scottalmond/NamePlate/src/jtag2updi/JTAG2.h

/*
 * packet.h
 *
 * Created: 12-11-2017 11:10:31
 *  Author: JMR_2
 */


#ifndef JTAG2_H_
#define JTAG2_H_

#include "sys.h"

namespace JTAG2 {

	// *** Parameter IDs ***
	enum parameter {
		PARAM_HW_VER				= 0x01,
		PARAM_FW_VER				= 0x02,
		PARAM_EMU_MODE				= 0x03,
		PARAM_BAUD_RATE				= 0x05,
		PARAM_VTARGET				= 0x06
	};

	// *** valid values for PARAM_BAUD_RATE_VAL
	enum baud_rate {
		baud_2400	= 0x01,
		baud_4800,
		baud_9600,
		baud_19200,				// default
		baud_38400,
		baud_57600,
		baud_115200,
		baud_14400
	};

	// *** Parameter Values ***
	constexpr uint8_t PARAM_HW_VER_M_VAL			= 0x01;
	constexpr uint8_t PARAM_HW_VER_S_VAL			= 0x01;
	constexpr uint8_t PARAM_FW_VER_M_MIN_VAL		= 0x00;
	constexpr uint8_t PARAM_FW_VER_M_MAJ_VAL		= 0x06;
	constexpr uint8_t PARAM_FW_VER_S_MIN_VAL		= 0x00;
	constexpr uint8_t PARAM_FW_VER_S_MAJ_VAL		= 0x06;
	extern uint8_t PARAM_EMU_MODE_VAL;
	extern uint8_t ConnectedTo;
	extern baud_rate PARAM_BAUD_RATE_VAL;
	constexpr uint16_t PARAM_VTARGET_VAL			= 5000;

	// *** General command constants ***
	enum cmnd {
		CMND_SIGN_OFF				= 0x00,
		CMND_GET_SIGN_ON			= 0x01,
		CMND_SET_PARAMETER			= 0x02,
		CMND_GET_PARAMETER			= 0x03,
		CMND_WRITE_MEMORY			= 0x04,
		CMND_READ_MEMORY			= 0x05,
		CMND_GO						= 0x08,
		CMND_RESET					= 0x0b,
		CMND_SET_DEVICE_DESCRIPTOR	= 0x0c,
		CMND_GET_SYNC				= 0x0f,
		CMND_ENTER_PROGMODE			= 0x14,
		CMND_LEAVE_PROGMODE			= 0x15,
		CMND_XMEGA_ERASE			= 0x34
	};
	// *** JTAG Mk2 Single byte status responses ***
	enum response {
		// Success
		RSP_OK						= 0x80,
		RSP_PARAMETER				= 0x81,
		RSP_MEMORY					= 0x82,
		RSP_SIGN_ON					= 0x86,
		// Error
		RSP_FAILED					= 0xA0,
		RSP_ILLEGAL_PARAMETER		= 0xA1,
		RSP_ILLEGAL_MEMORY_TYPE		= 0xA2,
		RSP_ILLEGAL_MEMORY_RANGE	= 0xA3,
		RSP_ILLEGAL_MCU_STATE		= 0xA5,
		RSP_ILLEGAL_VALUE			= 0xA6,
		RSP_ILLEGAL_BREAKPOINT		= 0xA8,
		RSP_ILLEGAL_JTAG_ID			= 0xA9,
		RSP_ILLEGAL_COMMAND			= 0xAA,
		RSP_NO_TARGET_POWER			= 0xAB,
		RSP_DEBUGWIRE_SYNC_FAILED	= 0xAC,
		RSP_ILLEGAL_POWER_STATE		= 0xAD
	};

	// *** memory types for CMND_{READ,WRITE}_MEMORY ***
	enum mem_type {
		MTYPE_IO_SHADOW				= 0x30,		// cached IO registers?
		MTYPE_SRAM					= 0x20,		// target's SRAM or [ext.] IO registers
		MTYPE_EEPROM				= 0x22,		// EEPROM, what way?
		MTYPE_EVENT					= 0x60,		// ICE event memory
		MTYPE_SPM					= 0xA0,		// flash through LPM/SPM
		MTYPE_FLASH_PAGE			= 0xB0,		// flash in programming mode
		MTYPE_EEPROM_PAGE			= 0xB1,		// EEPROM in programming mode
		MTYPE_FUSE_BITS				= 0xB2,		// fuse bits in programming mode
		MTYPE_LOCK_BITS				= 0xB3,		// lock bits in programming mode
		MTYPE_SIGN_JTAG				= 0xB4,		// signature in programming mode
		MTYPE_OSCCAL_BYTE			= 0xB5,		// osccal cells in programming mode
		MTYPE_CAN					= 0xB6,		// CAN mailbox
		MTYPE_FLASH					= 0xc0,		// xmega (app.) flash
		MTYPE_BOOT_FLASH			= 0xc1,		// xmega boot flash
		MTYPE_EEPROM_XMEGA			= 0xc4,		// xmega EEPROM in debug mode
		MTYPE_USERSIG				= 0xc5,		// xmega user signature
		MTYPE_PRODSIG				= 0xc6		// xmega production signature
	};

	// *** STK500 packet ***
	constexpr uint8_t MESSAGE_START = 0x1B;
	constexpr int MAX_BODY_SIZE = 700;				// Note: should not be reduced to less than 300 bytes.
	union packet_t {
		uint8_t raw[6 + MAX_BODY_SIZE];
		struct {
			union {
				uint16_t number;
				uint8_t number_byte[2];
			};
			union {
				uint32_t size;
				uint16_t size_word[2];
				uint8_t size_byte[4];
			};
			uint8_t body[MAX_BODY_SIZE];
		};
	} extern packet;
	constexpr uint8_t TOKEN = 0x0E;

	// *** Parameter initialization ***
	void init();

	// *** Packet functions ***
	bool receive();
	void answer();
	void delay_exec();

	// *** Set status function ***
	void set_status(uint8_t) __attribute__ ((noinline));

	// *** General command functions ***
	void sign_on();
	void get_parameter();
	void set_parameter();
	void set_device_descriptor();

	// *** ISP command functions ***
	void enter_progmode();
	void leave_progmode();
	void go();
	void read_signature();
	void read_mem();
	void write_mem();
	void erase();
}



#endif /* STK_H_ */
