scottalmond/NamePlate/src/test/atmel_touch_bak/atmel_touch_proj/atmel_touch_proj/include/atmel_start_pins.h

/*
 * Code generated from START.
 *
 * This file will be overwritten when reconfiguring your START project.
 * Please copy examples or other code you want to keep to a separate file
 * to avoid losing it when reconfiguring.
 */
#ifndef ATMEL_START_PINS_H_INCLUDED
#define ATMEL_START_PINS_H_INCLUDED

#include <port.h>

/**
 * \brief Set PIN_PA7 pull mode
 *
 * Configure pin to pull up, down or disable pull mode, supported pull
 * modes are defined by device used
 *
 * \param[in] pull_mode Pin pull mode
 */
static inline void PIN_PA7_set_pull_mode(const enum port_pull_mode pull_mode)
{
	PORTA_set_pin_pull_mode(7, pull_mode);
}

/**
 * \brief Set PIN_PA7 data direction
 *
 * Select if the pin data direction is input, output or disabled.
 * If disabled state is not possible, this function throws an assert.
 *
 * \param[in] direction PORT_DIR_IN  = Data direction in
 *                      PORT_DIR_OUT = Data direction out
 *                      PORT_DIR_OFF = Disables the pin
 *                      (low power state)
 */
static inline void PIN_PA7_set_dir(const enum port_dir dir)
{
	PORTA_set_pin_dir(7, dir);
}

/**
 * \brief Set PIN_PA7 input/sense configuration
 *
 * Enable/disable PIN_PA7 digital input buffer and pin change interrupt,
 * select pin interrupt edge/level sensing mode
 *
 * \param[in] isc PORT_ISC_INTDISABLE_gc    = Iterrupt disabled but input buffer enabled
 *                PORT_ISC_BOTHEDGES_gc     = Sense Both Edges
 *                PORT_ISC_RISING_gc        = Sense Rising Edge
 *                PORT_ISC_FALLING_gc       = Sense Falling Edge
 *                PORT_ISC_INPUT_DISABLE_gc = Digital Input Buffer disabled
 *                PORT_ISC_LEVEL_gc         = Sense low Level
 */
static inline void PIN_PA7_set_isc(const PORT_ISC_t isc)
{
	PORTA_pin_set_isc(7, isc);
}

/**
 * \brief Set PIN_PA7 inverted mode
 *
 * Enable or disable inverted I/O on a pin
 *
 * \param[in] inverted true  = I/O on PIN_PA7 is inverted
 *                     false = I/O on PIN_PA7 is not inverted
 */
static inline void PIN_PA7_set_inverted(const bool inverted)
{
	PORTA_pin_set_inverted(7, inverted);
}

/**
 * \brief Set PIN_PA7 level
 *
 * Sets output level on a pin
 *
 * \param[in] level true  = Pin level set to "high" state
 *                  false = Pin level set to "low" state
 */
static inline void PIN_PA7_set_level(const bool level)
{
	PORTA_set_pin_level(7, level);
}

/**
 * \brief Toggle output level on PIN_PA7
 *
 * Toggle the pin level
 */
static inline void PIN_PA7_toggle_level()
{
	PORTA_toggle_pin_level(7);
}

/**
 * \brief Get level on PIN_PA7
 *
 * Reads the level on a pin
 */
static inline bool PIN_PA7_get_level()
{
	return PORTA_get_pin_level(7);
}

/**
 * \brief Set PIN_PB0 pull mode
 *
 * Configure pin to pull up, down or disable pull mode, supported pull
 * modes are defined by device used
 *
 * \param[in] pull_mode Pin pull mode
 */
static inline void PIN_PB0_set_pull_mode(const enum port_pull_mode pull_mode)
{
	PORTB_set_pin_pull_mode(0, pull_mode);
}

/**
 * \brief Set PIN_PB0 data direction
 *
 * Select if the pin data direction is input, output or disabled.
 * If disabled state is not possible, this function throws an assert.
 *
 * \param[in] direction PORT_DIR_IN  = Data direction in
 *                      PORT_DIR_OUT = Data direction out
 *                      PORT_DIR_OFF = Disables the pin
 *                      (low power state)
 */
static inline void PIN_PB0_set_dir(const enum port_dir dir)
{
	PORTB_set_pin_dir(0, dir);
}

/**
 * \brief Set PIN_PB0 input/sense configuration
 *
 * Enable/disable PIN_PB0 digital input buffer and pin change interrupt,
 * select pin interrupt edge/level sensing mode
 *
 * \param[in] isc PORT_ISC_INTDISABLE_gc    = Iterrupt disabled but input buffer enabled
 *                PORT_ISC_BOTHEDGES_gc     = Sense Both Edges
 *                PORT_ISC_RISING_gc        = Sense Rising Edge
 *                PORT_ISC_FALLING_gc       = Sense Falling Edge
 *                PORT_ISC_INPUT_DISABLE_gc = Digital Input Buffer disabled
 *                PORT_ISC_LEVEL_gc         = Sense low Level
 */
static inline void PIN_PB0_set_isc(const PORT_ISC_t isc)
{
	PORTB_pin_set_isc(0, isc);
}

/**
 * \brief Set PIN_PB0 inverted mode
 *
 * Enable or disable inverted I/O on a pin
 *
 * \param[in] inverted true  = I/O on PIN_PB0 is inverted
 *                     false = I/O on PIN_PB0 is not inverted
 */
static inline void PIN_PB0_set_inverted(const bool inverted)
{
	PORTB_pin_set_inverted(0, inverted);
}

/**
 * \brief Set PIN_PB0 level
 *
 * Sets output level on a pin
 *
 * \param[in] level true  = Pin level set to "high" state
 *                  false = Pin level set to "low" state
 */
static inline void PIN_PB0_set_level(const bool level)
{
	PORTB_set_pin_level(0, level);
}

/**
 * \brief Toggle output level on PIN_PB0
 *
 * Toggle the pin level
 */
static inline void PIN_PB0_toggle_level()
{
	PORTB_toggle_pin_level(0);
}

/**
 * \brief Get level on PIN_PB0
 *
 * Reads the level on a pin
 */
static inline bool PIN_PB0_get_level()
{
	return PORTB_get_pin_level(0);
}

/**
 * \brief Set PB2 pull mode
 *
 * Configure pin to pull up, down or disable pull mode, supported pull
 * modes are defined by device used
 *
 * \param[in] pull_mode Pin pull mode
 */
static inline void PB2_set_pull_mode(const enum port_pull_mode pull_mode)
{
	PORTB_set_pin_pull_mode(2, pull_mode);
}

/**
 * \brief Set PB2 data direction
 *
 * Select if the pin data direction is input, output or disabled.
 * If disabled state is not possible, this function throws an assert.
 *
 * \param[in] direction PORT_DIR_IN  = Data direction in
 *                      PORT_DIR_OUT = Data direction out
 *                      PORT_DIR_OFF = Disables the pin
 *                      (low power state)
 */
static inline void PB2_set_dir(const enum port_dir dir)
{
	PORTB_set_pin_dir(2, dir);
}

/**
 * \brief Set PB2 input/sense configuration
 *
 * Enable/disable PB2 digital input buffer and pin change interrupt,
 * select pin interrupt edge/level sensing mode
 *
 * \param[in] isc PORT_ISC_INTDISABLE_gc    = Iterrupt disabled but input buffer enabled
 *                PORT_ISC_BOTHEDGES_gc     = Sense Both Edges
 *                PORT_ISC_RISING_gc        = Sense Rising Edge
 *                PORT_ISC_FALLING_gc       = Sense Falling Edge
 *                PORT_ISC_INPUT_DISABLE_gc = Digital Input Buffer disabled
 *                PORT_ISC_LEVEL_gc         = Sense low Level
 */
static inline void PB2_set_isc(const PORT_ISC_t isc)
{
	PORTB_pin_set_isc(2, isc);
}

/**
 * \brief Set PB2 inverted mode
 *
 * Enable or disable inverted I/O on a pin
 *
 * \param[in] inverted true  = I/O on PB2 is inverted
 *                     false = I/O on PB2 is not inverted
 */
static inline void PB2_set_inverted(const bool inverted)
{
	PORTB_pin_set_inverted(2, inverted);
}

/**
 * \brief Set PB2 level
 *
 * Sets output level on a pin
 *
 * \param[in] level true  = Pin level set to "high" state
 *                  false = Pin level set to "low" state
 */
static inline void PB2_set_level(const bool level)
{
	PORTB_set_pin_level(2, level);
}

/**
 * \brief Toggle output level on PB2
 *
 * Toggle the pin level
 */
static inline void PB2_toggle_level()
{
	PORTB_toggle_pin_level(2);
}

/**
 * \brief Get level on PB2
 *
 * Reads the level on a pin
 */
static inline bool PB2_get_level()
{
	return PORTB_get_pin_level(2);
}

/**
 * \brief Set PB3 pull mode
 *
 * Configure pin to pull up, down or disable pull mode, supported pull
 * modes are defined by device used
 *
 * \param[in] pull_mode Pin pull mode
 */
static inline void PB3_set_pull_mode(const enum port_pull_mode pull_mode)
{
	PORTB_set_pin_pull_mode(3, pull_mode);
}

/**
 * \brief Set PB3 data direction
 *
 * Select if the pin data direction is input, output or disabled.
 * If disabled state is not possible, this function throws an assert.
 *
 * \param[in] direction PORT_DIR_IN  = Data direction in
 *                      PORT_DIR_OUT = Data direction out
 *                      PORT_DIR_OFF = Disables the pin
 *                      (low power state)
 */
static inline void PB3_set_dir(const enum port_dir dir)
{
	PORTB_set_pin_dir(3, dir);
}

/**
 * \brief Set PB3 input/sense configuration
 *
 * Enable/disable PB3 digital input buffer and pin change interrupt,
 * select pin interrupt edge/level sensing mode
 *
 * \param[in] isc PORT_ISC_INTDISABLE_gc    = Iterrupt disabled but input buffer enabled
 *                PORT_ISC_BOTHEDGES_gc     = Sense Both Edges
 *                PORT_ISC_RISING_gc        = Sense Rising Edge
 *                PORT_ISC_FALLING_gc       = Sense Falling Edge
 *                PORT_ISC_INPUT_DISABLE_gc = Digital Input Buffer disabled
 *                PORT_ISC_LEVEL_gc         = Sense low Level
 */
static inline void PB3_set_isc(const PORT_ISC_t isc)
{
	PORTB_pin_set_isc(3, isc);
}

/**
 * \brief Set PB3 inverted mode
 *
 * Enable or disable inverted I/O on a pin
 *
 * \param[in] inverted true  = I/O on PB3 is inverted
 *                     false = I/O on PB3 is not inverted
 */
static inline void PB3_set_inverted(const bool inverted)
{
	PORTB_pin_set_inverted(3, inverted);
}

/**
 * \brief Set PB3 level
 *
 * Sets output level on a pin
 *
 * \param[in] level true  = Pin level set to "high" state
 *                  false = Pin level set to "low" state
 */
static inline void PB3_set_level(const bool level)
{
	PORTB_set_pin_level(3, level);
}

/**
 * \brief Toggle output level on PB3
 *
 * Toggle the pin level
 */
static inline void PB3_toggle_level()
{
	PORTB_toggle_pin_level(3);
}

/**
 * \brief Get level on PB3
 *
 * Reads the level on a pin
 */
static inline bool PB3_get_level()
{
	return PORTB_get_pin_level(3);
}

#endif /* ATMEL_START_PINS_H_INCLUDED */
