scottalmond/NamePlate/src/test/atmel_blink/simple_blink/simple_blink/src/driver_init.c

/**
 * \file
 *
 * \brief Driver initialization.
 *
 (c) 2018 Microchip Technology Inc. and its subsidiaries.

    Subject to your compliance with these terms,you may use this software and
    any derivatives exclusively with Microchip products.It is your responsibility
    to comply with third party license terms applicable to your use of third party
    software (including open source software) that may accompany Microchip software.

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
    IN NO EVENT WILL MICROCHIP BE LIABLE FOR ANY INDIRECT, SPECIAL, PUNITIVE,
    INCIDENTAL OR CONSEQUENTIAL LOSS, DAMAGE, COST OR EXPENSE OF ANY KIND
    WHATSOEVER RELATED TO THE SOFTWARE, HOWEVER CAUSED, EVEN IF MICROCHIP HAS
    BEEN ADVISED OF THE POSSIBILITY OR THE DAMAGES ARE FORESEEABLE. TO THE
    FULLEST EXTENT ALLOWED BY LAW, MICROCHIP'S TOTAL LIABILITY ON ALL CLAIMS IN
    ANY WAY RELATED TO THIS SOFTWARE WILL NOT EXCEED THE AMOUNT OF FEES, IF ANY,
    THAT YOU HAVE PAID DIRECTLY TO MICROCHIP FOR THIS SOFTWARE.
 *
 */

/*
 * Code generated by START.
 *
 * This file will be overwritten when reconfiguring your START project.
 * Please copy examples or other code you want to keep to a separate file
 * to avoid losing it when reconfiguring.
 */

#include "driver_init.h"
#include <system.h>

/**
 * \brief System initialization
 */
void system_init()
{
	mcu_init();

	/* PORT setting on PA7 */

	// Set pin direction to output

	PIN_PA7_set_level(
	    // <y> Initial level
	    // <id> pad_initial_level
	    // <false"> Low
	    // <true"> High
	    false);

	PIN_PA7_set_dir(PORT_DIR_OUT);

	CLKCTRL_init();

	CPUINT_init();

	SLPCTRL_init();

	BOD_init();
}
